Lukas0025/SatteliteRotator/SW_Rotator/easycomm.h

#pragma ones

#include <Arduino.h>

class easycomm {

private:
  Stream *serial_port;

public:
  int ComAzim = 0;
  int ComElev = 0;

  easycomm(Stream *serial_port) { this->serial_port = serial_port; }

  void parse(int TruAzim, int TruElev);
};
